Gaurav-ece/led-matrix-hourglass/images/image2.jpeg

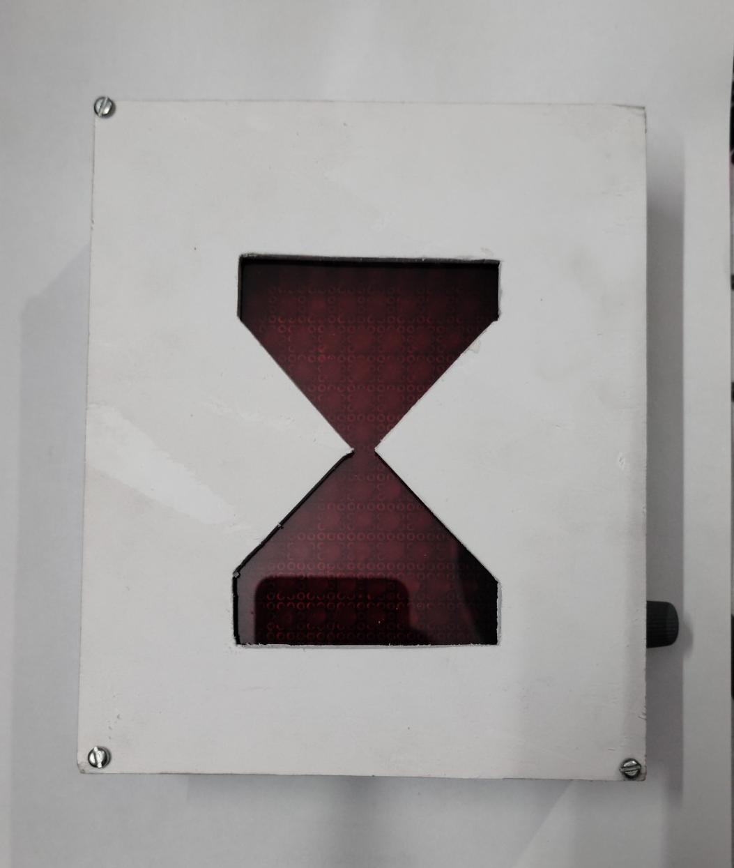
images/image2.jpeg
