Gaurav-ece/led-matrix-hourglass/schematic/hourglass.kicad_sch

## KiCad design schematic/hourglass.kicad_sch (2026-07-05)

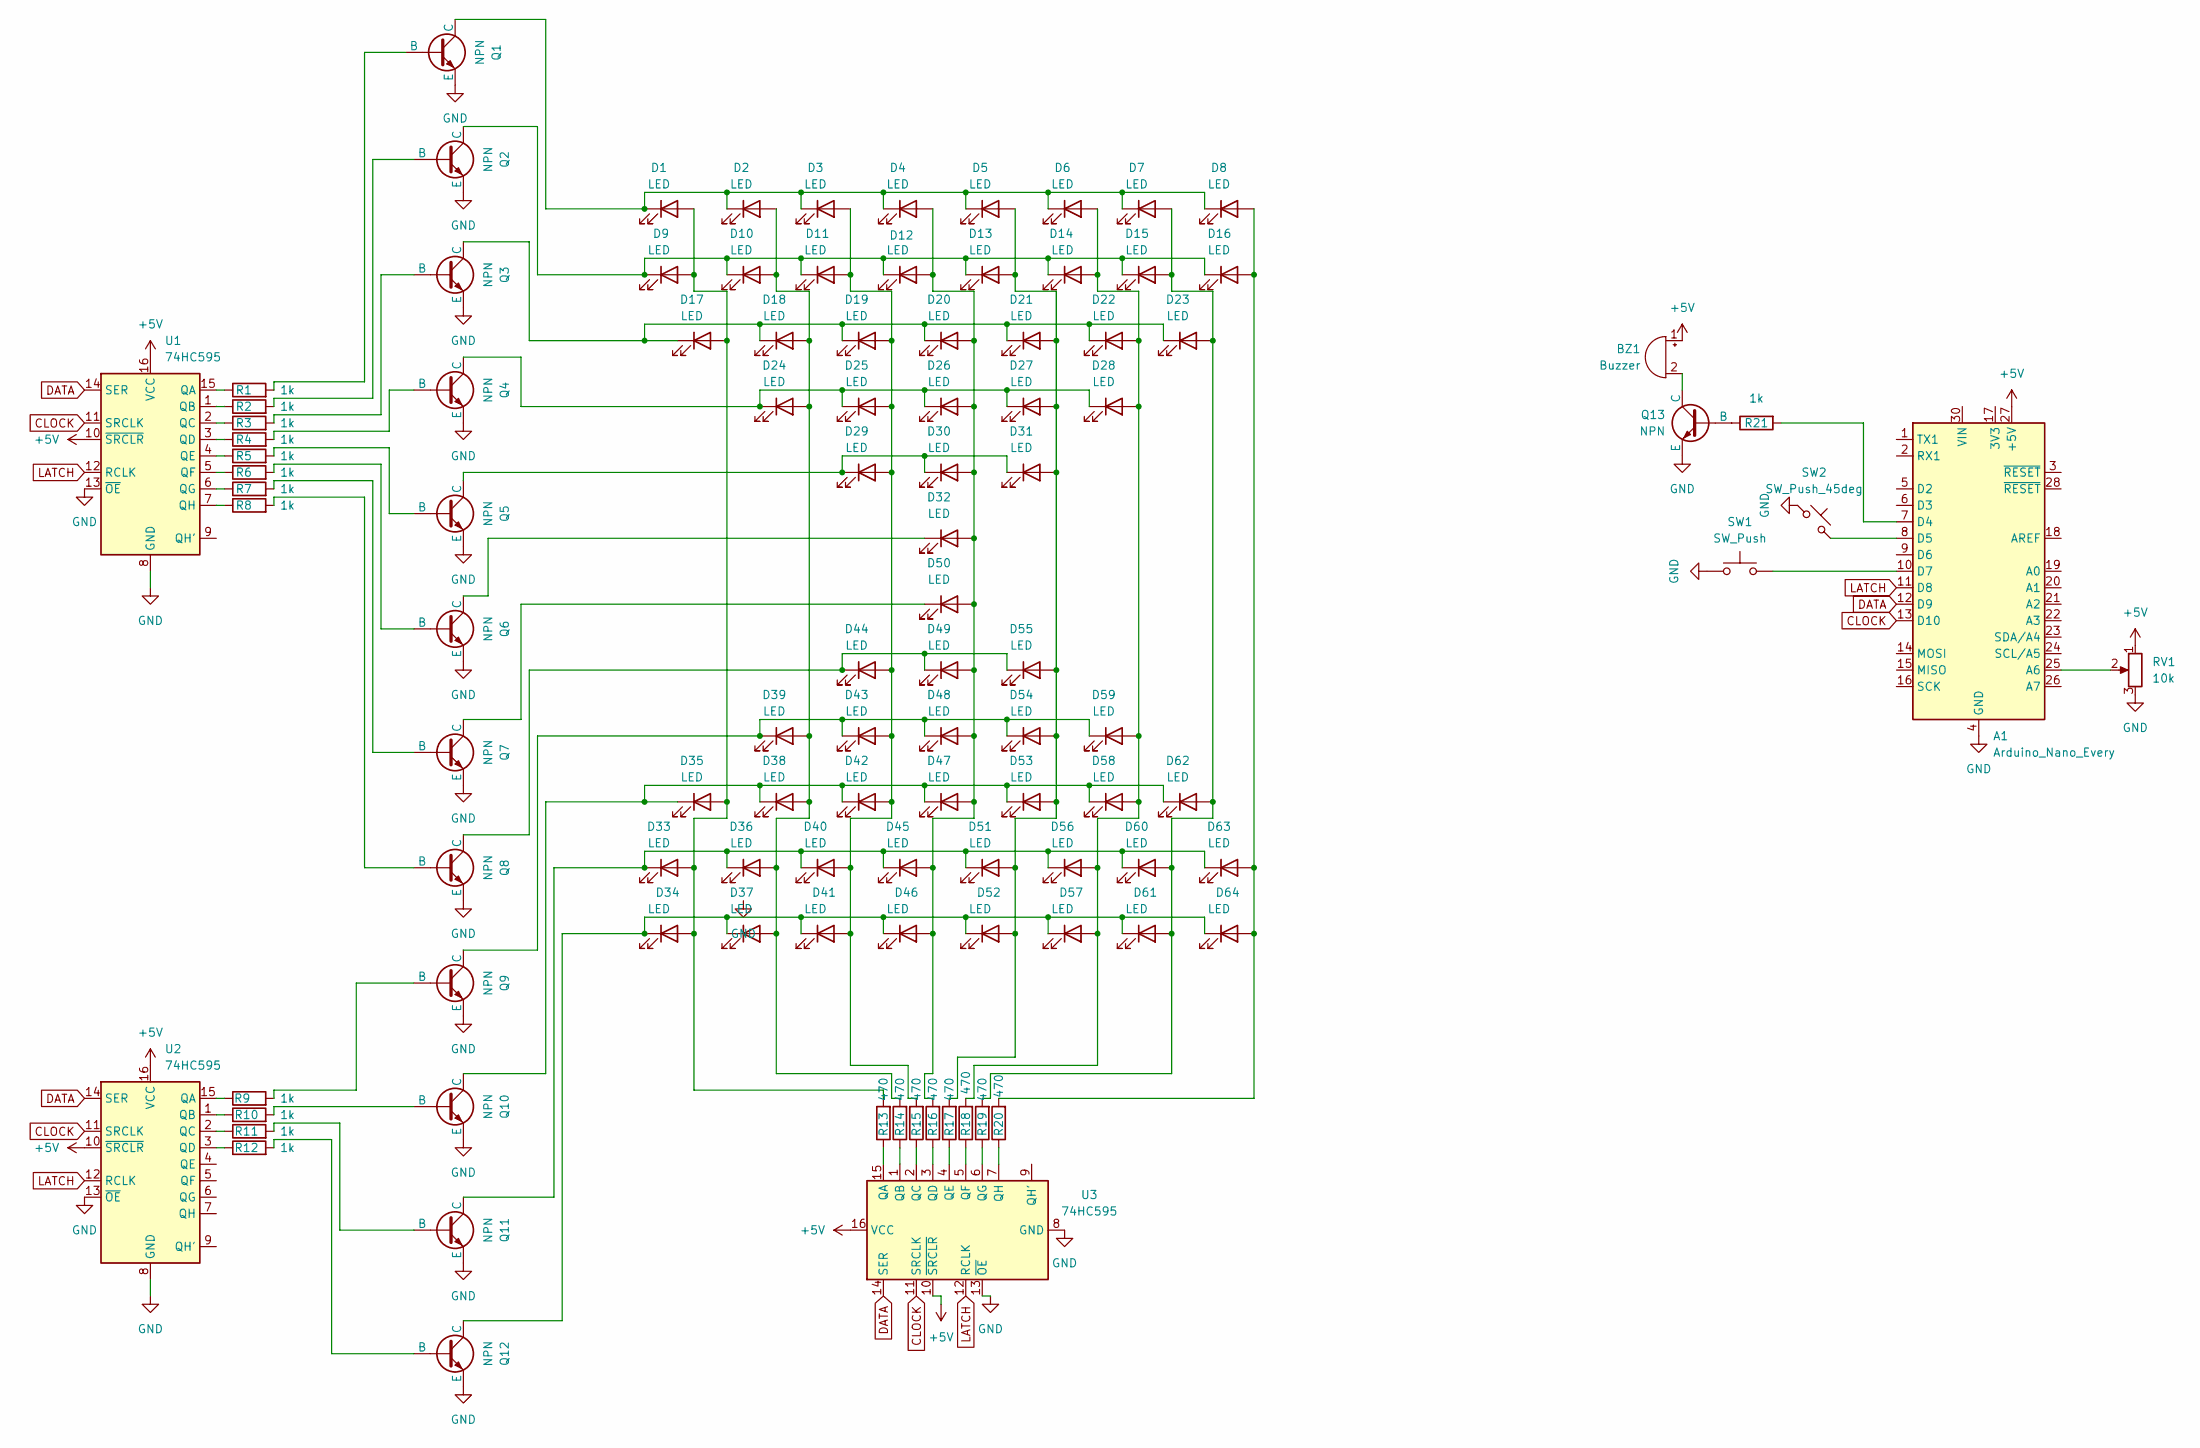
[picture p6: schematic hourglass.kicad_sch]

Parts:
A1: Arduino_Nano_Every; Arduino_Nano
BZ1: Buzzer
D1, D2, D3, D4, D5, D6, D7, D8, D9, D10, D11, D12, D13, D14, D15, D16, D17, D18, D19, D20, D21, D22, D23, D24, D25, D26, D27, D28, D29, D30, D31, D32, D33, D34, D35, D36, D37, D38, D39, D40, D41, D42, D43, D44, D45, D46, D47, D48, D49, D50, D51, D52, D53, D54, D55, D56, D57, D58, D59, D60, D61, D62, D63, D64: LED
Q1, Q2, Q3, Q4, Q5, Q6, Q7, Q8, Q9, Q10, Q11, Q12, Q13: NPN
R1, R2, R3, R4, R5, R6, R7, R8, R9, R10, R11, R12, R21: 1k
R13, R14, R15, R16, R17, R18, R19, R20: 470
RV1: 10k
SW1: SW_Push
SW2: SW_Push_45deg
U1, U2, U3: 74HC595

Connections:
+5V: A1.27 (+5V), BZ1.1 (+), RV1.1, U1.10 (~SRCLR), U1.16 (VCC), U2.10 (~SRCLR), U2.16 (VCC), U3.10 (~SRCLR), U3.16 (VCC)
CLOCK: A1.13 (D10), U1.11 (SRCLK), U2.11 (SRCLK), U3.11 (SRCLK)
DATA: A1.12 (D9), U1.14 (SER), U2.14 (SER), U3.14 (SER)
GND: A1.4 (GND), A1.29 (GND), Q1.3 (E), Q2.3 (E), Q3.3 (E), Q4.3 (E), Q5.3 (E), Q6.3 (E), Q7.3 (E), Q8.3 (E), Q9.3 (E), Q10.3 (E), Q11.3 (E), Q12.3 (E), Q13.3 (E), RV1.3, SW1.1, SW2.1, U1.8 (GND), U1.13 (~OE), U2.8 (GND), U2.13 (~OE), U3.8 (GND), U3.13 (~OE)
LATCH: A1.11 (D8), U1.12 (RCLK), U2.12 (RCLK), U3.12 (RCLK)
unnamed: A1.7 (D4), R21.2
unnamed: A1.8 (D5), SW2.2
unnamed: A1.10 (D7), SW1.2
unnamed: A1.25 (A6), RV1.2
unnamed: BZ1.2 (-), Q13.1 (C)
unnamed: D1.1 (K), D2.1 (K), D3.1 (K), D4.1 (K), D5.1 (K), D6.1 (K), D7.1 (K), D8.1 (K), Q1.1 (C)
unnamed: D1.2 (A), D9.2 (A), D17.2 (A), D33.2 (A), D34.2 (A), D35.2 (A), R13.2
unnamed: D9.1 (K), D10.1 (K), D11.1 (K), D12.1 (K), D13.1 (K), D14.1 (K), D15.1 (K), D16.1 (K), Q2.1 (C)
unnamed: D2.2 (A), D10.2 (A), D18.2 (A), D24.2 (A), D36.2 (A), D37.2 (A), D38.2 (A), D39.2 (A), R14.2
unnamed: D3.2 (A), D11.2 (A), D19.2 (A), D25.2 (A), D29.2 (A), D40.2 (A), D41.2 (A), D42.2 (A), D43.2 (A), D44.2 (A), R15.2
unnamed: D4.2 (A), D12.2 (A), D20.2 (A), D26.2 (A), D30.2 (A), D32.2 (A), D45.2 (A), D46.2 (A), D47.2 (A), D48.2 (A), D49.2 (A), D50.2 (A), R16.2
unnamed: D5.2 (A), D13.2 (A), D21.2 (A), D27.2 (A), D31.2 (A), D51.2 (A), D52.2 (A), D53.2 (A), D54.2 (A), D55.2 (A), R17.2
unnamed: D6.2 (A), D14.2 (A), D22.2 (A), D28.2 (A), D56.2 (A), D57.2 (A), D58.2 (A), D59.2 (A), R18.2
unnamed: D7.2 (A), D15.2 (A), D23.2 (A), D60.2 (A), D61.2 (A), D62.2 (A), R19.2
unnamed: D8.2 (A), D16.2 (A), D63.2 (A), D64.2 (A), R20.2
unnamed: D17.1 (K), D18.1 (K), D19.1 (K), D20.1 (K), D21.1 (K), D22.1 (K), D23.1 (K), Q3.1 (C)
unnamed: D24.1 (K), D25.1 (K), D26.1 (K), D27.1 (K), D28.1 (K), Q4.1 (C)
unnamed: D29.1 (K), D30.1 (K), D31.1 (K), Q5.1 (C)
unnamed: D32.1 (K), Q6.1 (C)
unnamed: D33.1 (K), D36.1 (K), D40.1 (K), D45.1 (K), D51.1 (K), D56.1 (K), D60.1 (K), D63.1 (K), Q11.1 (C)
unnamed: D34.1 (K), D37.1 (K), D41.1 (K), D46.1 (K), D52.1 (K), D57.1 (K), D61.1 (K), D64.1 (K), Q12.1 (C)
unnamed: D35.1 (K), D38.1 (K), D42.1 (K), D47.1 (K), D53.1 (K), D58.1 (K), D62.1 (K), Q10.1 (C)
unnamed: D39.1 (K), D43.1 (K), D48.1 (K), D54.1 (K), D59.1 (K), Q9.1 (C)
unnamed: D44.1 (K), D49.1 (K), D55.1 (K), Q8.1 (C)
unnamed: D50.1 (K), Q7.1 (C)
unnamed: Q1.2 (B), R1.2
unnamed: Q2.2 (B), R2.2
unnamed: Q3.2 (B), R3.2
unnamed: Q4.2 (B), R4.2
unnamed: Q5.2 (B), R5.2
unnamed: Q6.2 (B), R6.2
unnamed: Q7.2 (B), R7.2
unnamed: Q8.2 (B), R8.2
unnamed: Q9.2 (B), R9.2
unnamed: Q10.2 (B), R10.2
unnamed: Q11.2 (B), R11.2
unnamed: Q12.2 (B), R12.2
unnamed: Q13.2 (B), R21.1
unnamed: R1.1, U1.15 (QA)
unnamed: R2.1, U1.1 (QB)
unnamed: R3.1, U1.2 (QC)
unnamed: R4.1, U1.3 (QD)
unnamed: R5.1, U1.4 (QE)
unnamed: R6.1, U1.5 (QF)
unnamed: R7.1, U1.6 (QG)
unnamed: R8.1, U1.7 (QH)
unnamed: R9.1, U2.15 (QA)
unnamed: R10.1, U2.1 (QB)
unnamed: R11.1, U2.2 (QC)
unnamed: R12.1, U2.3 (QD)
unnamed: R13.1, U3.15 (QA)
unnamed: R14.1, U3.1 (QB)
unnamed: R15.1, U3.2 (QC)
unnamed: R16.1, U3.3 (QD)
unnamed: R17.1, U3.4 (QE)
unnamed: R18.1, U3.5 (QF)
unnamed: R19.1, U3.6 (QG)
unnamed: R20.1, U3.7 (QH)
